PrasannahRam/ANALOG_COMPUTER/Drafts/Draft2 (1).asc

C1: cap; 10µ
D1: diode
D2: diode
D3: diode
D4: diode
D5: diode
R1: res; 10k
R2: res; 10k
R3: res; 10k
R4: res; 10k
R5: res; 10k
R6: res; 10k
R7: res; 10k
R8: res; 10k
R9: res; 10k
R10: res; 10k
R11: res; 10k
R12: res; 10k
R13: res; 680k
R14: res; 33k
U1: NE5532
U2: NE5532
U3: NE5532
U4: NE5532
U5: NE5532
U6: NE5532
U7: NE5532
V1: voltage; 15
V2: voltage; 15
V3: voltage; SINE(0 4 10000 0 0)
V4: voltage; SINE(0 3 10000 0 0)
V5: voltage; 1
Named nets: 0, -Vcc, +Vcc
.tran 0 35m 14m
