PrasannahRam/ANALOG_COMPUTER/Drafts/Gilbert Multiplier V1.asc

C1: cap; 0,1u
C2: cap; 0,1u
C3: cap; 0.1µ
C4: cap; 1µ
C5: cap; 1µ
Q1: npn; 2N3904
Q2: npn; 2N3904
Q3: npn; 2N3904
Q4: npn; 2N3904
Q5: npn; 2N3904
Q6: npn; 2N3904
R1: res; 270
R2: res; 270
R3: res; 270
R4: res; 4.7k
R5: res; 3.3k
R6: res; 2.2k
R7: res; 2.2k
R8: res; 2.2k
R9: res; 2.2k
R10: res; 2.2k
R11: res; 50
R12: res; 50
V1: voltage; 12
V2: voltage; 12
V3: voltage; 12
V4: voltage; SINE(0 0.2 100k 0 0 0)
V5: voltage; SINE(0 0.3 10k 0 0 0)
Named nets: 0
.tran 1m
