PrasannahRam/ANALOG_COMPUTER/Drafts/Multiplier.asc

C1: cap; 10µf
D1: diode
D2: diode
D3: diode
R1: res; 10k
R2: res; 10k
R3: res; 10k
R4: res; 10k
R5: res; 10k
R6: res; 10k
R7: res; 4k
R8: res; 4k
R9: res; 10k
R10: res; 10k
R11: res; 10k
U1: opamp2; NE5532
U2: opamp2; NE5532
U3: opamp2; NE5532
U4: opamp2; NE5532
U5: opamp2; NE5532
V1: voltage; 15
V2: voltage; 15
V3: voltage; SINE(2.5 0.5 100 0 0 0)
V4: voltage; SINE(2.5 0.5 100 0 0 0)
Named nets: 0, V1, V2, -Vcc, +Vcc
.tran 100m
.include NE5532.lib
