PrasannahRam/ANALOG_COMPUTER/Drafts/Multiplier_final_edited.asc

C2: cap; 1µ
C4: cap; 1µ
C5: cap; 1µ
Q1: npn; 2N3904
Q2: npn; 2N3904
Q3: npn; 2N3904
Q4: npn; 2N3904
Q5: npn; 2N3904
Q6: npn; 2N3904
R1: res; 270
R2: res; 270
R3: res; 270
R4: res; 4.7k
R5: res; 3.3k
R6: res; 2.2k
R7: res; 2.2k
R8: res; 2.2k
R9: res; 2.2k
R10: res; 2.2k
R11: res; 10k
R12: res; 10k
R13: res; 1k
R14: res; 1k
R15: res; 10k
R16: res; 1k
R17: res; 10k
R19: res; 1k
R20: res; 1k
R21: res; 1k
U4: NE5532
U5: NE5532
V1: voltage; 12
V4: voltage; SINE(0 0.125 10)
V5: voltage; SINE(0 1.25 1)
V6: voltage; 15
V7: voltage; 15
Named nets: 0, +V, -V, V1, V2, Vout
.tran 10
