PrasannahRam/ANALOG_COMPUTER/Simulations/substractor.asc

R1: res; 10K; tol=1 pwr=0.1
R2: res; 10K; tol=1 pwr=0.1
R3: res; 10K; tol=1 pwr=0.1
R4: res; 10K; tol=1 pwr=0.1
U1: opamp2; ne5532
V1: voltage; SINE(0 2 10k)
V2: voltage; SINE(0 5 10k)
V3: voltage; 15
V4: voltage; -15
Named nets: 0
.lib ne5532.sub
.tran 5m
